EbenAET/Orciny-Device/circuit/kicad/orciny wiring RevB/orciny wiring RevB.kicad_pcb

## KiCad design electronic-exp-01-oscillator-integrator.kicad_sch

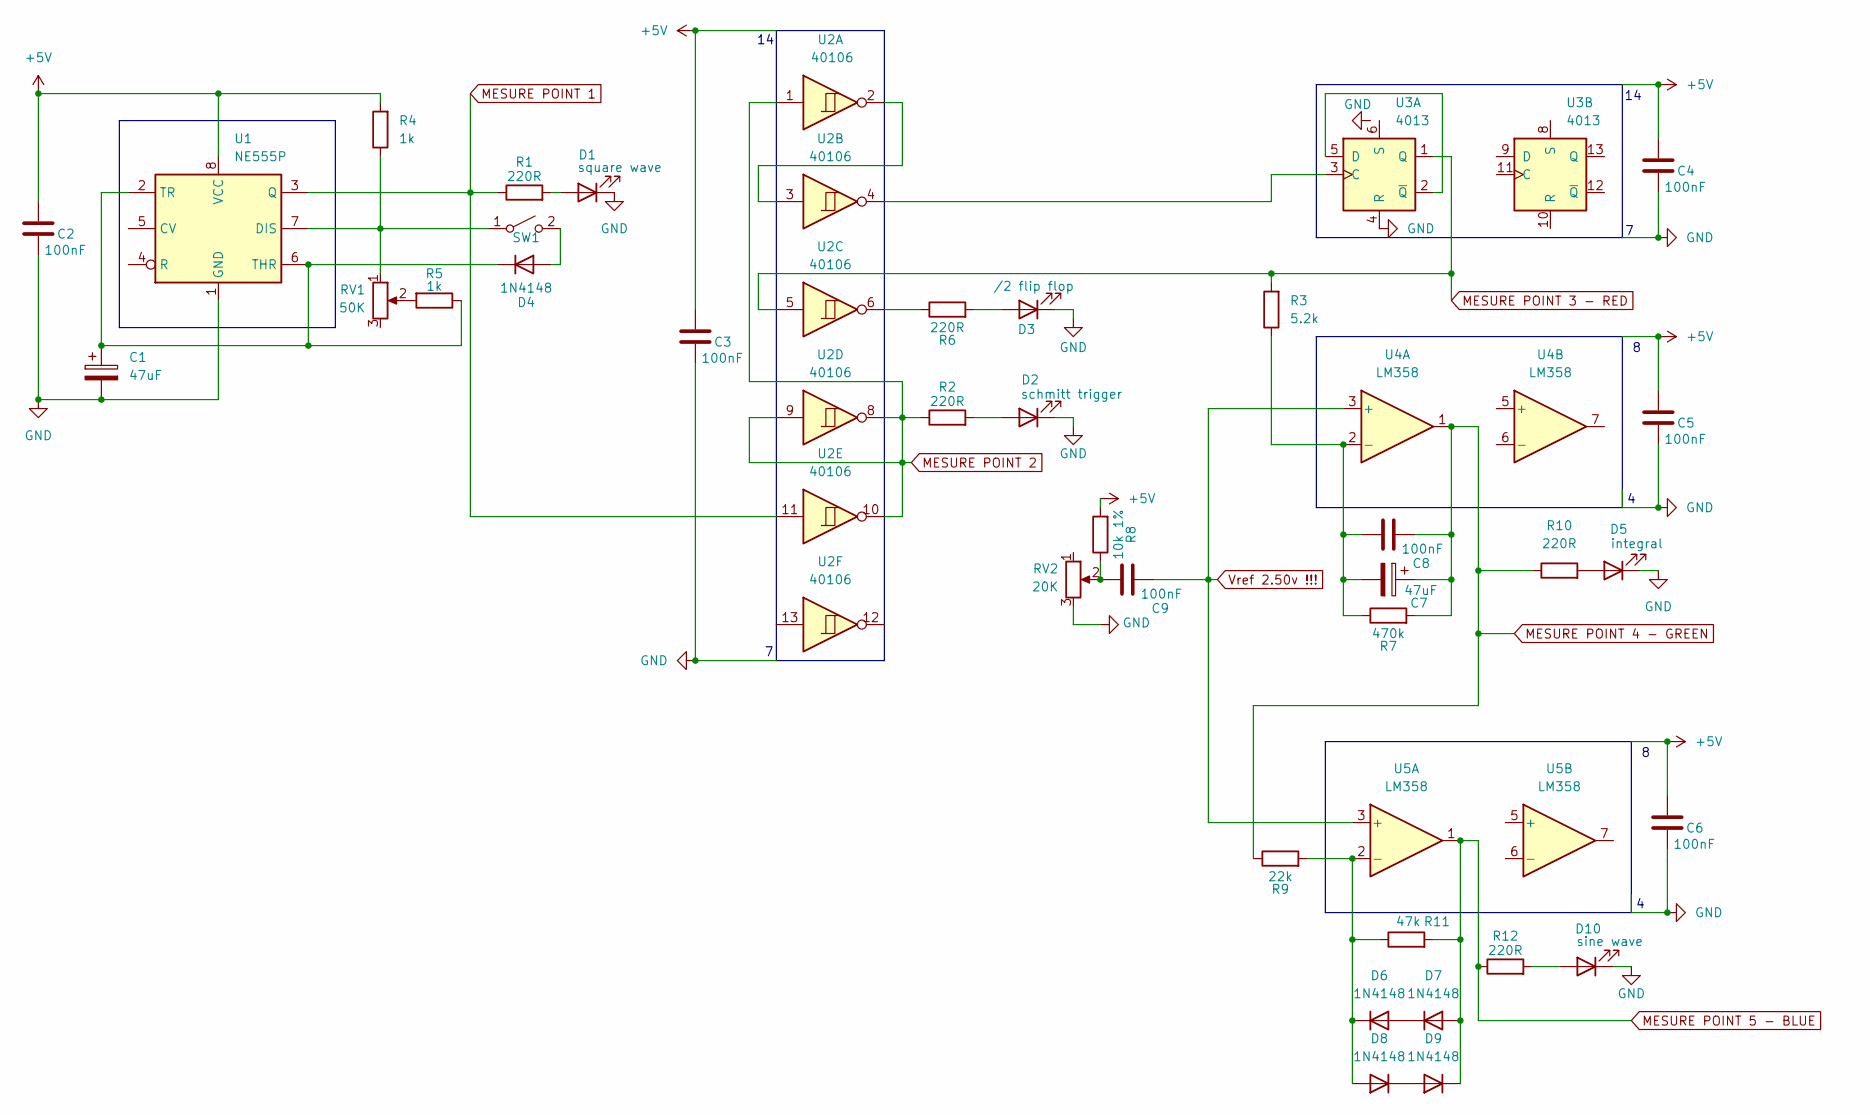
[picture p8: schematic electronic-exp-01-oscillator-integrator.kicad_sch]

Parts:
C1, C7: 47uF
C2, C3, C4, C5, C6, C8, C9: 100nF
D1: square wave
D2: schmitt trigger
D3: /2 flip flop
D4, D6, D7, D8, D9: 1N4148; D_DO-35_SOD27_P7.62mm_Horizontal
D5: integral
D10: sine wave
R1, R2, R6, R10, R12: 220R
R3: 5.2k
R4, R5: 1k
R7: 470k
R8: 10k 1%
R9: 22k
R11: 47k
RV1: 50K
RV2: 20K
SW1: (no value)
U1: NE555P; DIP-8_W7.62mm
U2: 40106
U3: 4013
U4, U5: LM358

Connections:
+5V: C2.1, C3.1, C4.1, C5.1, C6.1, R4.2, R8.2, U1.8 (VCC)
GND: C1.2, C2.2, C3.2, C4.2, C5.2, C6.2, D1.1 (K), D2.1 (K), D3.1 (K), D5.1 (K), D10.1 (K), RV2.3, U1.1 (GND), U3.4 (R)
MESURE POINT 1: R1.1, U1.3 (Q), U2.11
MESURE POINT 2: R2.1, U2.1, U2.8, U2.9, U2.10
MESURE POINT 3 - RED: R3.2, U2.5, U3.1 (Q)
MESURE POINT 4 - GREEN: C7.1, C8.1, R7.2, R9.1, R10.1, U4.1
MESURE POINT 5 - BLUE: D7.2 (A), D9.1 (K), R11.2, R12.1, U5.1
unnamed: C1.1, D4.1 (K), R5.1, U1.2 (TR), U1.6 (THR)
unnamed: C7.2, C8.2, R3.1, R7.1, U4.2 (-)
unnamed: C9.2, R8.1, RV2.2
unnamed: D1.2 (A), R1.2
unnamed: D2.2 (A), R2.2
unnamed: D3.2 (A), R6.2
unnamed: D4.2 (A), SW1.2 (B)
unnamed: D5.2 (A), R10.2
unnamed: D6.1 (K), D8.2 (A), R9.2, R11.1, U5.2 (-)
unnamed: D6.2 (A), D7.1 (K)
unnamed: D8.1 (K), D9.2 (A)
unnamed: D10.2 (A), R12.2
unnamed: R4.1, RV1.1, SW1.1 (A), U1.7 (DIS)
unnamed: R5.2, RV1.2
unnamed: R6.1, U2.6
unnamed: U2.2, U2.3
unnamed: U2.4, U3.3 (C)
unnamed: U3.2 (~Q), U3.5 (D)
Vref 2.50v !!!: C9.1, U4.3 (+), U5.3 (+)
