EbenAET/Orciny-Device/Arduino/rp2040_fx_controller_demo/rp2040_fx_controller_demo.ino

// =============================================================================
// rp2040_fx_controller_demo.ino
// Version : V 0.2.5
// Orciny Device — FX Controller  |  Demo / Testing Build
// Board : Adafruit Feather RP2040
// Wings : Prop-Maker FeatherWing + 8-Channel Servo FeatherWing (PCA9685)
// -----------------------------------------------------------------------------
// PURPOSE
//   This is the fully-commented demo version of the main FX controller sketch.
//   All logic is identical to the production sketch; comments have been added
//   throughout to explain every section for anyone reviewing or testing it.
//
// CONTROL PATH
//   Standalone mode only.
//   handleSwitches(), handleUsbCommands(), and buildActiveProfile() drive all
//   outputs directly from the physical buttons and USB serial commands.
//
// USB SERIAL COMMANDS (115200 baud, standalone mode)
//   help            — list all commands
//   status          — print power, sequence, and effect overrides
//   on / off        — enable or disable all outputs
//   toggle          — flip current output state
//   prev / next     — step through sequences
//   seq1 / seq2 / seq3 — jump directly to a numbered sequence
//   reset           — return to sequence 1, output off
//   sparks on|off|toggle|auto — per-effect override
//   spark1|spark2|spark3|spark4 on|off — force one spark channel for bench test
//   spark all on|off — force all spark channels on/off for bench test
//   spark status — print spark test mode and GPIO mapping
//   beam on|off|toggle|auto   — per-effect override
//   claw on|off|toggle|auto   — per-effect override
//   peltier on|off|auto|status — GP8 MOSFET gate override/test
//   red|green|blue on|off|toggle|auto — per-channel beam overrides
//   s|bm|c on|off|toggle|auto — short aliases for sparks|beam|claw
//   r|g|b on|off|toggle|auto  — short aliases for red|green|blue
//   beam palette cool|ember|cyan|violet|auto — beam colour palette
//   buttons         — print raw and debounced switch states
//   servoa/servob min|max|mid — direct PCA9685 channel test writes
//   neo on|off      — turn all pixels on (white) or off
//   neo color <R G B> [BRIGHT] — set all pixels to RGB color (0-255 each)
//   neo ember|pulse|beam|claw|show — test specific animation modes
//   neo auto        — follow scene default (stop testing)
//
// PHYSICAL CONTROLS
//   SW1 (A1 / GP27) — tap: toggle output on/off          (standalone only)
//   SW2 (A2 / GP28) — tap: step to previous sequence     (standalone only)
//   SW3 (A3 / GP29) — tap: step to next sequence         (standalone only)
//   SW1 + SW3 held 5 s — reset to sequence 1             (standalone only)
//
// DEMO SEQUENCES
//   1 — Ember  : sparks on, warm-orange NeoPixel ember glow    (beam: ember palette)
//   2 — Pulse  : beam pulsing, orange NeoPixel pulse           (beam: cool-white palette)
//   3 — Show   : sparks + beam + claw sweep, cyan NeoPixel     (beam: cyan palette)
// =============================================================================

#include <Adafruit_PWMServoDriver.h>  // PCA9685 servo wing driver
#include <Adafruit_NeoPixel.h>        // NeoPixel strip driver
#include <Wire.h>                     // I2C bus (required by servo driver)

#include <OrcinyCommon.h>              // Shared packet types: CoreFrame, EffectCommand, etc.
#include <ColorPalettes.h>             // Beam and NeoPixel color palettes
#include <AnimationPalettes.h>         // Animation preset definitions

#include "DeviceConfig.h"  // All pin assignments and tuning constants

// Pull frequently-used types into this file's scope so we don't have to
// prefix every usage with "orciny::".
using orciny::CoreFrame;
using orciny::EffectCommand;
using orciny::CoreMode;

// =============================================================================
// SEQUENCE IDs
// A SequenceId is just a named number.  It identifies which "scene" is active
// and drives the content of buildActiveProfile() below.
// =============================================================================
enum SequenceId : uint8_t {
  SEQUENCE_1 = 0,   // Ember scene
  SEQUENCE_2,       // Pulse scene
  SEQUENCE_3,       // Full show scene
  SEQUENCE_COUNT,   // Automatically equals the number of sequences (3)
};

// =============================================================================
// BEAM PALETTE IDs
// Named identifiers for the built-in beam colour palettes defined in
// DeviceConfig.h.  BEAM_PALETTE_AUTO means "use whatever the active scene
// requests"; the other values lock the palette regardless of scene.
// =============================================================================
enum BeamPaletteId : uint8_t {
  BEAM_PALETTE_AUTO = 0,   // follow the scene's palette selection
  BEAM_PALETTE_COOL,       // cool white (original swell colour)
  BEAM_PALETTE_EMBER,      // warm orange-red
  BEAM_PALETTE_CYAN,       // pure cyan
  BEAM_PALETTE_VIOLET,     // purple-violet
};

// Return the DeviceConfig palette for a given BeamPaletteId.
// BEAM_PALETTE_AUTO resolves to kPaletteCoolWhite (same as the original default).
const device_config::BeamPalette &getPaletteForId(BeamPaletteId id) {
  switch (id) {
    case BEAM_PALETTE_EMBER:  return device_config::kPaletteEmber;
    case BEAM_PALETTE_CYAN:   return device_config::kPaletteCyan;
    case BEAM_PALETTE_VIOLET: return device_config::kPaletteViolet;
    default:                  return device_config::kPaletteCoolWhite;
  }
}

// =============================================================================
// SceneProfile
// A flat data record that describes what every output subsystem should be doing
// for the currently active sequence.  buildActiveProfile() fills one of these;
// profileToEffectCommand() converts it into a wire-format EffectCommand.
// =============================================================================
struct SceneProfile {
  bool          sparksEnabled;
  uint8_t       sparksIntensity;   // 0–255 PWM brightness of random spark flashes
  bool          beamEnabled;       // Prop-Maker LED beam on/off
  bool          clawEnabled;       // Servo claw sweep on/off
  BeamPaletteId beamPaletteId;     // colour palette for the beam swell
  CoreFrame     coreFrame;         // NeoPixel core parameters (mode, color, speed…)
};

// =============================================================================
// MomentarySwitch
// Wraps a single digital input with software debouncing.
//
// Why debounce?  Mechanical switches bounce — the contacts open and close
// rapidly for ~5–20 ms after a press.  Without debouncing, one physical press
// can register as many events.  This class ignores transitions shorter than
// kSwitchDebounceMs before accepting them as stable.
//
// Usage:
//   switch.begin(PIN);         // call once in setup()
//   switch.update(millis());   // call every loop iteration
//   if (switch.wasPressed())   // true for exactly one loop after press
// =============================================================================
class MomentarySwitch {
 public:
  void begin(uint8_t pin) {
    pin_ = pin;
    pinMode(pin_, INPUT_PULLUP);  // Internal pull-up: floating = HIGH, pressed = LOW
    // Sample the physical state immediately so the first update() is accurate.
    const bool initialPressed = (digitalRead(pin_) == LOW);
    stablePressed_ = initialPressed;
    rawPressed_ = initialPressed;
    lastChangeMs_ = millis();
  }

  // Call once per loop iteration with the current millis() timestamp.
  void update(uint32_t now) {
    // Reset single-shot flags at the start of every update.
    pressedEvent_ = false;
    releasedEvent_ = false;

    const bool sampledPressed = (digitalRead(pin_) == LOW);

    // If the raw reading changed, restart the debounce timer.
    if (sampledPressed != rawPressed_) {
      rawPressed_ = sampledPressed;
      lastChangeMs_ = now;
    }

    // Wait for the signal to be stable for the full debounce window.
    if ((now - lastChangeMs_) < device_config::kSwitchDebounceMs) {
      return;  // Still within bouncing window — do nothing yet.
    }

    // If the stable state already matches the raw reading, nothing changed.
    if (stablePressed_ == rawPressed_) {
      return;
    }

    // The state changed and has been stable long enough — accept it.
    stablePressed_ = rawPressed_;
    if (stablePressed_) {
      pressedEvent_ = true;   // Fires on the loop after the press settles.
    } else {
      releasedEvent_ = true;  // Fires on the loop after the release settles.
    }
  }

  bool isPressed() const  { return stablePressed_; }  // Current stable state
  bool wasPressed() const { return pressedEvent_; }   // True for one loop on press
  bool wasReleased() const { return releasedEvent_; } // True for one loop on release

 private:
  uint8_t  pin_ = 0;
  bool     stablePressed_  = false;
  bool     rawPressed_     = false;
  bool     pressedEvent_   = false;
  bool     releasedEvent_  = false;
  uint32_t lastChangeMs_   = 0;
};

// =============================================================================
// SparkChannel
// Drives one GPIO pin with random PWM bursts to simulate a spark-gap element.
//
// Each channel independently decides when to fire and for how long using
// random timing windows.  The intensity parameter scales the peak brightness
// and also raises the floor so sparks never go completely dark during a flash.
// =============================================================================
class SparkChannel {
 public:
  void begin(uint8_t pin) {
    pin_ = pin;
    pinMode(pin_, OUTPUT);
    analogWrite(pin_, 0);  // Start off
    // Stagger the first event so all four channels don't fire simultaneously.
    nextEventMs_ = millis() + random(30, 180);
  }

  // enabled   : false forces pin low immediately and reschedules.
  // intensity : 0–255 PWM ceiling for peak brightness.
  void update(uint32_t now, bool enabled, uint8_t intensity) {
    if (!enabled) {
      analogWrite(pin_, 0);
      active_ = false;
      // Longer cool-down when disabled to prevent instant re-fire on enable.
      nextEventMs_ = now + random(80, 200);
      return;
    }

    if (active_) {
      // Currently in a flash burst — check whether the burst has expired.
      if (now >= flashUntilMs_) {
        active_ = false;
        analogWrite(pin_, 0);
        nextEventMs_ = now + random(25, 140);  // Random gap before next flash
      }
      return;  // Mid-burst: nothing to do until expiry.
    }

    // Waiting between flashes — check if it's time to fire.
    if (now < nextEventMs_) {
      return;
    }

    // Fire!  Choose a random PWM value between a floor and the intensity cap.
    const int minimum = max(32, intensity / 3);   // Minimum brightness floor
    const int peak    = max(minimum + 1, static_cast<int>(intensity) + 1);
    analogWrite(pin_, random(minimum, peak));
    // Hold the flash for a random short duration (20–70 ms).
    flashUntilMs_ = now + random(20, 71);
    active_ = true;
  }

  void setManualLevel(uint8_t level) {
    analogWrite(pin_, level);
    active_ = (level > 0);
  }

 private:
  uint8_t  pin_          = 0;
  bool     active_       = false;
  uint32_t nextEventMs_  = 0;
  uint32_t flashUntilMs_ = 0;
};

// =============================================================================
// BeamEffect
// Drives the three Prop-Maker MOSFET channels (Red/Green/Blue) with a slow
// sinusoidal swell whose colour is defined by a BeamPalette.
//
// The swell is computed from millis() so it runs continuously without a
// separate state machine.
//
// How the swell works:
//   • phase = (now % 2400) gives a 2.4-second repeating window (0–2399).
//   • First half (0–1199): linearly ramps from 100 → 255 (brightening).
//   • Second half (1200–2399): linearly ramps from 255 → 100 (dimming).
//   • Each RGB channel is scaled: output = (swell × palette.channel) / 255.
//   • Call setPalette() to change colour; defaults to kPaletteDefault.
// =============================================================================
class BeamEffect {
 public:
  void begin(uint8_t led1Pin, uint8_t led2Pin, uint8_t led3Pin) {
    redPin_   = led1Pin;
    greenPin_ = led2Pin;
    bluePin_  = led3Pin;
    pinMode(redPin_,   OUTPUT);
    pinMode(greenPin_, OUTPUT);
    pinMode(bluePin_,  OUTPUT);
    stop();
  }

  // Change the active colour palette.  Takes effect on the next update() call.
  void setPalette(const device_config::BeamPalette &palette) {
    currentPalette_ = palette;
  }

  void update(uint32_t now, bool enabled) {
    if (!enabled) {
      stop();
      return;
    }

    const uint16_t phase = now % 2400;  // 2.4-second cycle

    // Linear ramp up then down, staying in the 100–255 range.
    const uint8_t swell = phase < 1200
                          ? map(phase, 0,    1200, 100, 255)
                          : map(phase, 1200, 2400, 255, 100);

    // Scale each channel by (swell / 255) × palette peak value.
    const uint16_t s = swell;
    analogWrite(redPin_,   static_cast<uint8_t>((s * currentPalette_.red)   / 255));
    analogWrite(greenPin_, static_cast<uint8_t>((s * currentPalette_.green) / 255));
    analogWrite(bluePin_,  static_cast<uint8_t>((s * currentPalette_.blue)  / 255));
    active_ = true;
  }

  void stop() {
    analogWrite(redPin_,   0);
    analogWrite(greenPin_, 0);
    analogWrite(bluePin_,  0);
    active_ = false;
  }

 private:
  uint8_t redPin_   = 0;
  uint8_t greenPin_ = 0;
  uint8_t bluePin_  = 0;
  bool    active_   = false;
  device_config::BeamPalette currentPalette_ = device_config::kPaletteDefault;
};

// =============================================================================
// ClawEffect
// Drives two servo channels on the PCA9685 in a continuous back-and-forth sweep.
//
// Servo A sweeps from minAngleA to maxAngleA and back.
// Servo B mirrors Servo A using a cross-mapped angle so both claw halves open
// and close together (one going up while the other goes down).
//
// The step interval (kClawStepIntervalMs) controls how fast the claw sweeps.
// Each update() call advances the angle by exactly one degree if the interval
// has elapsed — no delays or blocking waits.
// =============================================================================
class ClawEffect {
 public:
  void begin(Adafruit_PWMServoDriver &driver,
             uint8_t servoChannelA, uint8_t servoChannelB,
             uint8_t minAngleA,    uint8_t maxAngleA,
             uint8_t minAngleB,    uint8_t maxAngleB) {
    driver_        = &driver;
    servoChannelA_ = servoChannelA;
    servoChannelB_ = servoChannelB;
    // Ensure min < max regardless of which way the caller passed them.
    minAngleA_ = min(minAngleA, maxAngleA);
    maxAngleA_ = max(minAngleA, maxAngleA);
    minAngleB_ = min(minAngleB, maxAngleB);
    maxAngleB_ = max(minAngleB, maxAngleB);
    angle_     = minAngleA_;
    direction_ = 1;             // Start sweeping toward maxAngleA_
    active_    = false;
    wasEnabled_ = false;
    if (device_config::kServoIdleWhenInactive) {
      idleServos();
    } else {
      writeServos(static_cast<uint8_t>(angle_));
      active_ = true;
    }
  }

  void update(uint32_t now, bool enabled) {
    if (!enabled) {
      if (wasEnabled_) {
        stop();
      }
      wasEnabled_ = false;
      return;
    }

    if (!wasEnabled_) {
      writeServos(static_cast<uint8_t>(angle_));
      nextStepMs_  = now + device_config::kClawStepIntervalMs;
      active_      = true;
      wasEnabled_  = true;
      return;
    }

    // Non-blocking timer: only advance one step after the interval elapses.
    if (now < nextStepMs_) {
      return;
    }

    angle_ += direction_;

    // Reverse direction at each travel limit.
    if (angle_ >= maxAngleA_) {
      angle_     = maxAngleA_;
      direction_ = -1;
    } else if (angle_ <= minAngleA_) {
      angle_     = minAngleA_;
      direction_ = 1;
    }

    writeServos(static_cast<uint8_t>(angle_));
    nextStepMs_ = now + device_config::kClawStepIntervalMs;
    active_ = true;
  }

  // Disable or park claw servos when motion is inactive.
  void stop() {
    if (!active_) {
      return;  // Already stopped — avoid redundant I2C writes.
    }

    if (device_config::kServoIdleWhenInactive) {
      idleServos();
    } else {
      writeServos(minAngleA_);
    }

    active_ = false;
  }

 private:
  // Convert a 0–180° angle to the PCA9685 pulse-count range.
  uint16_t angleToPulse(uint8_t angle) const {
    return map(angle, 0, 180,
               device_config::kServoMinPulse,
               device_config::kServoMaxPulse);
  }

  // Mirror Servo A's angle onto Servo B's range so they move in opposition.
  uint8_t mapAngleForB(uint8_t angleA) const {
    return map(angleA, minAngleA_, maxAngleA_, maxAngleB_, minAngleB_);
  }

  // Push both servo positions to the PCA9685 over I2C.
  void writeServos(uint8_t angleA) {
    if (driver_ == nullptr) {
      return;
    }
    const uint8_t clampedA = constrain(angleA, minAngleA_, maxAngleA_);
    const uint8_t angleB   = constrain(mapAngleForB(clampedA), minAngleB_, maxAngleB_);
    driver_->setPWM(servoChannelA_, 0, angleToPulse(clampedA));
    driver_->setPWM(servoChannelB_, 0, angleToPulse(angleB));
  }

  // PCA9685 off command for a channel: ON=0/OFF=0 disables pulses.
  void idleServos() {
    if (driver_ == nullptr) {
      return;
    }
    driver_->setPWM(servoChannelA_, 0, 0);
    driver_->setPWM(servoChannelB_, 0, 0);
  }

  Adafruit_PWMServoDriver *driver_ = nullptr;
  uint8_t  servoChannelA_ = 0;
  uint8_t  servoChannelB_ = 1;
  int16_t  angle_         = 0;
  uint8_t  minAngleA_     = 0;
  uint8_t  maxAngleA_     = 180;
  uint8_t  minAngleB_     = 0;
  uint8_t  maxAngleB_     = 180;
  int8_t   direction_     = 1;
  bool     active_        = false;
  bool     wasEnabled_    = false;
  uint32_t nextStepMs_    = 0;
};

// =============================================================================
// GLOBAL INSTANCES
// One object per physical subsystem.  All are initialized in setup().
// =============================================================================

SparkChannel sparks[device_config::kSparkCount];  // Four independent spark channels
BeamEffect   beamEffect;                           // Prop-Maker RGB beam
ClawEffect   clawEffect;                           // Dual-servo claw
Adafruit_PWMServoDriver servoDriver(device_config::kServoDriverI2cAddress);
Adafruit_NeoPixel neoPixelStrip(device_config::kNeoPixelCount,
                                device_config::kNeoPixelPin,
                                device_config::kNeoPixelType);

MomentarySwitch powerSwitch;    // SW1 — on/off toggle
MomentarySwitch previousSwitch; // SW2 — previous sequence
MomentarySwitch nextSwitch;     // SW3 — next sequence

// =============================================================================
// GLOBAL STATE VARIABLES
// These track the runtime state; they are manipulated by the standalone-mode
// control functions (handleSwitches, handleUsbCommands).
// =============================================================================

SequenceId currentSequence      = SEQUENCE_1;  // Which scene is active
bool       outputEnabled        = false;         // Master on/off flag

enum EffectOverride : uint8_t {
  OVERRIDE_AUTO = 0,
  OVERRIDE_FORCE_OFF,
  OVERRIDE_FORCE_ON,
};

EffectOverride sparksOverride = OVERRIDE_AUTO;
EffectOverride beamOverride   = OVERRIDE_AUTO;
EffectOverride clawOverride   = OVERRIDE_AUTO;
EffectOverride peltierOverride = OVERRIDE_AUTO;
EffectOverride beamRedOverride   = OVERRIDE_AUTO;
EffectOverride beamGreenOverride = OVERRIDE_AUTO;
EffectOverride beamBlueOverride  = OVERRIDE_AUTO;
int8_t sparkTestSelection = -1;  // -1=auto, 0..3=single channel, 4=all channels

// Active beam palette override.  BEAM_PALETTE_AUTO uses the active scene's default.
BeamPaletteId beamPaletteOverride = BEAM_PALETTE_AUTO;

// Active NeoPixel frame override. Mode OFF means "use scene default".
CoreFrame neoPixelOverride = orciny::defaultFrame();

// USB receive buffer — characters accumulate here until a newline is received.
String usbCommandBuffer;

uint32_t peltierHoldUntilMs  = 0;  // Keep cooling active briefly after beam-off

// Standalone-only build always reports standalone mode.
bool standaloneMode = true;

bool     suppressPreviousRelease = false;

// State for the SW1+SW3 reset chord (standalone mode only).
uint32_t resetChordStartMs    = 0;
bool     resetChordTriggered  = false;
bool     suppressPowerRelease = false;  // Prevent toggle fire after chord hold
bool     suppressNextRelease  = false;  // Prevent seq advance after chord hold

// =============================================================================
// UTILITY — status printing
// =============================================================================

// Print a list of available USB serial commands.
void printHelp() {
  Serial.println(F("Commands: help, status, on, off, toggle, prev, next, seq1, seq2, seq3, reset"));
  Serial.println(F("         sparks on|off|toggle|auto"));
  Serial.println(F("         spark1|spark2|spark3|spark4 on|off"));
  Serial.println(F("         spark all on|off"));
  Serial.println(F("         spark status"));
  Serial.println(F("         beam   on|off|toggle|auto"));
  Serial.println(F("         claw   on|off|toggle|auto"));
  Serial.println(F("         peltier on|off|auto|status"));
  Serial.println(F("         red|green|blue on|off|toggle|auto"));
  Serial.println(F("         s|bm|c and r|g|b on|off|toggle|auto"));
  Serial.println(F("         beam palette cool|ember|cyan|violet|auto"));
  Serial.println(F("         buttons"));
  Serial.println(F("         servoa min|max|mid"));
  Serial.println(F("         servob min|max|mid"));
  Serial.println(F("         neo on|off|color <R G B> [BRIGHT]"));
  Serial.println(F("         neo ember|pulse|beam|claw|show|auto"));
}

uint16_t servoAngleToPulse(uint8_t angle) {
  return map(angle, 0, 180, device_config::kServoMinPulse, device_config::kServoMaxPulse);
}

void writeServoTest(uint8_t channel, uint8_t angle) {
  servoDriver.setPWM(channel, 0, servoAngleToPulse(angle));
  Serial.print(F("Servo CH"));
  Serial.print(channel);
  Serial.print(F(" -> angle "));
  Serial.println(angle);
}

void printButtonSnapshot() {
  const bool rawSw1Pressed = digitalRead(device_config::kPowerSwitchPin) == LOW;
  const bool rawSw2Pressed = digitalRead(device_config::kPreviousSwitchPin) == LOW;
  const bool rawSw3Pressed = digitalRead(device_config::kNextSwitchPin) == LOW;

  Serial.print(F("Buttons raw      -> SW1:"));
  Serial.print(rawSw1Pressed ? F("P") : F("R"));
  Serial.print(F(" SW2:"));
  Serial.print(rawSw2Pressed ? F("P") : F("R"));
  Serial.print(F(" SW3:"));
  Serial.println(rawSw3Pressed ? F("P") : F("R"));

  Serial.print(F("Buttons debounced-> SW1:"));
  Serial.print(powerSwitch.isPressed() ? F("P") : F("R"));
  Serial.print(F(" SW2:"));
  Serial.print(previousSwitch.isPressed() ? F("P") : F("R"));
  Serial.print(F(" SW3:"));
  Serial.println(nextSwitch.isPressed() ? F("P") : F("R"));
}

const __FlashStringHelper *overrideLabel(EffectOverride value) {
  switch (value) {
    case OVERRIDE_FORCE_OFF: return F("FORCE_OFF");
    case OVERRIDE_FORCE_ON:  return F("FORCE_ON");
    default:                 return F("AUTO");
  }
}

bool applyOverride(bool baseState, EffectOverride value) {
  if (value == OVERRIDE_FORCE_ON) {
    return true;
  }
  if (value == OVERRIDE_FORCE_OFF) {
    return false;
  }
  return baseState;
}

bool isSparkTestActive() {
  return sparkTestSelection >= 0;
}

bool isSparkTestChannelEnabled(uint8_t index) {
  return sparkTestSelection == device_config::kSparkCount ||
         sparkTestSelection == static_cast<int8_t>(index);
}

void printSparkTestStatus() {
  if (!isSparkTestActive()) {
    Serial.println(F("Spark test -> AUTO"));
    return;
  }

  if (sparkTestSelection == device_config::kSparkCount) {
    Serial.println(F("Spark test -> ALL ON"));
    return;
  }

  Serial.print(F("Spark test -> CH"));
  Serial.print(sparkTestSelection + 1);
  Serial.println(F(" ON"));
}

void printSparkPinMap() {
  Serial.print(F("Spark pins -> CH1:GP"));
  Serial.print(device_config::kSparkPins[0]);
  Serial.print(F(" CH2:GP"));
  Serial.print(device_config::kSparkPins[1]);
  Serial.print(F(" CH3:GP"));
  Serial.print(device_config::kSparkPins[2]);
  Serial.print(F(" CH4:GP"));
  Serial.println(device_config::kSparkPins[3]);
}

void printSparkStatus() {
  printSparkTestStatus();
  printSparkPinMap();
}

void printPeltierStatus() {
  Serial.print(F("Peltier -> "));
  Serial.print(overrideLabel(peltierOverride));
  Serial.print(F(", GP"));
  Serial.print(device_config::kPeltierControlPin);
  Serial.print(F(" pin is "));
  Serial.println(digitalRead(device_config::kPeltierControlPin) == HIGH ? F("HIGH") : F("LOW"));
}

void printModeStatus() {
  Serial.println(F("Mode -> STANDALONE"));
}

void printOverrideStatus() {
  Serial.print(F("Overrides -> sparks: "));
  Serial.print(overrideLabel(sparksOverride));
  Serial.print(F(", beam: "));
  Serial.print(overrideLabel(beamOverride));
  Serial.print(F(", claw: "));
  Serial.print(overrideLabel(clawOverride));
  Serial.print(F(", peltier: "));
  Serial.println(overrideLabel(peltierOverride));

  Serial.print(F("Beam RGB -> R: "));
  Serial.print(overrideLabel(beamRedOverride));
  Serial.print(F(", G: "));
  Serial.print(overrideLabel(beamGreenOverride));
  Serial.print(F(", B: "));
  Serial.println(overrideLabel(beamBlueOverride));

  const __FlashStringHelper *palLabel;
  switch (beamPaletteOverride) {
    case BEAM_PALETTE_COOL:   palLabel = F("cool");   break;
    case BEAM_PALETTE_EMBER:  palLabel = F("ember");  break;
    case BEAM_PALETTE_CYAN:   palLabel = F("cyan");   break;
    case BEAM_PALETTE_VIOLET: palLabel = F("violet"); break;
    default:                  palLabel = F("auto");   break;
  }
  Serial.print(F("Beam palette -> "));
  Serial.println(palLabel);
  printSparkTestStatus();
}

// Print the current power state and sequence number to USB serial.
void printSequenceStatus() {
  printModeStatus();
  Serial.print(F("Power -> "));
  Serial.print(outputEnabled ? F("ON") : F("OFF"));
  Serial.print(F(", Sequence -> "));
  Serial.println(static_cast<uint8_t>(currentSequence) + 1);
  printOverrideStatus();
  printButtonSnapshot();
}

// =============================================================================
// SCENE PROFILES
// buildActiveProfile() is the heart of standalone mode.  It maps the current
// (outputEnabled, currentSequence) state to a full SceneProfile that describes
// what every subsystem should do.
//
// Add or modify cases here to change what each button-selectable scene does.
// This function is the active profile source for this standalone-only build.
// =============================================================================
SceneProfile buildActiveProfile() {
  SceneProfile profile = {};
  profile.coreFrame = orciny::defaultFrame();

  // Output off — zero everything and return early.
  if (!outputEnabled) {
    profile.coreFrame.mode       = orciny::CORE_MODE_OFF;
    profile.coreFrame.brightness = 0;
    return profile;
  }

  switch (currentSequence) {

    // --- SEQUENCE 1: Ember ---------------------------------------------------
    // Sparks flash at high intensity.  NeoPixel glows a warm orange ember.
    case SEQUENCE_1:
      profile.sparksEnabled    = true;
      profile.sparksIntensity  = 220;
      profile.beamPaletteId        = BEAM_PALETTE_EMBER;
      profile.coreFrame.mode       = orciny::CORE_MODE_EMBER;
      profile.coreFrame.brightness = 56;
      profile.coreFrame.speed      = 90;
      profile.coreFrame.red        = 255;
      profile.coreFrame.green      = 110;
      profile.coreFrame.blue       = 24;
      return profile;

    // --- SEQUENCE 2: Pulse ---------------------------------------------------
    // Beam lamp cycles on/off.  NeoPixel pulses in a cooler orange.
    case SEQUENCE_2:
      profile.beamEnabled          = true;
      profile.beamPaletteId        = BEAM_PALETTE_COOL;
      profile.coreFrame.mode       = orciny::CORE_MODE_PULSE;
      profile.coreFrame.brightness = 96;
      profile.coreFrame.speed      = 110;
      profile.coreFrame.red        = 255;
      profile.coreFrame.green      = 48;
      profile.coreFrame.blue       = 0;
      return profile;

    // --- SEQUENCE 3: Full Show -----------------------------------------------
    // Everything on: sparks at max, beam running, claw sweeping, NeoPixel show.
    case SEQUENCE_3:
      profile.sparksEnabled    = true;
      profile.sparksIntensity  = 255;
      profile.beamEnabled      = true;
      profile.beamPaletteId    = BEAM_PALETTE_CYAN;
      profile.clawEnabled      = true;
      profile.coreFrame.mode       = orciny::CORE_MODE_SHOW;
      profile.coreFrame.brightness = 180;
      profile.coreFrame.speed      = 140;
      profile.coreFrame.red        = 60;
      profile.coreFrame.green      = 220;
      profile.coreFrame.blue       = 255;
      return profile;

    default:
      profile.coreFrame.mode       = orciny::CORE_MODE_OFF;
      profile.coreFrame.brightness = 0;
      return profile;
  }
}

// Convert a SceneProfile into an EffectCommand so updateEffects() can consume
// a single, consistent command structure.
EffectCommand profileToEffectCommand(const SceneProfile &profile) {
  EffectCommand command = orciny::defaultEffectCommand();
  command.outputEnabled   = outputEnabled;
  command.sparksEnabled   = applyOverride(profile.sparksEnabled, sparksOverride);
  command.sparksIntensity = command.sparksEnabled
                            ? (profile.sparksIntensity > 0 ? profile.sparksIntensity : 220)
                            : 0;
  command.pulseEnabled    = false;  // Not used in current hardware
  command.beamEnabled     = applyOverride(profile.beamEnabled, beamOverride);
  command.clawEnabled     = applyOverride(profile.clawEnabled, clawOverride);
  return command;
}

// =============================================================================
// SEQUENCE NAVIGATION HELPERS
// =============================================================================

SequenceId previousSequenceValue(SequenceId sequence) {
  // Wrap around: sequence 1 → wraps back to sequence 3.
  return sequence == SEQUENCE_1 ? SEQUENCE_3
                                : static_cast<SequenceId>(sequence - 1);
}

SequenceId nextSequenceValue(SequenceId sequence) {
  // Wrap around: sequence 3 → wraps back to sequence 1.
  return sequence == SEQUENCE_3 ? SEQUENCE_1
                                : static_cast<SequenceId>(sequence + 1);
}

void setSequence(SequenceId sequence) {
  currentSequence = sequence;
  printSequenceStatus();  // Echo new state to USB serial
}

void resetToBeginning() {
  currentSequence = SEQUENCE_1;
  outputEnabled = false;
  sparksOverride = OVERRIDE_AUTO;
  beamOverride = OVERRIDE_AUTO;
  clawOverride = OVERRIDE_AUTO;
  peltierOverride = OVERRIDE_AUTO;
  beamRedOverride = OVERRIDE_AUTO;
  beamGreenOverride = OVERRIDE_AUTO;
  beamBlueOverride = OVERRIDE_AUTO;
  beamPaletteOverride = BEAM_PALETTE_AUTO;
  Serial.println(F("Reset -> sequence 1"));
  printSequenceStatus();
}

// =============================================================================
// STANDALONE MODE — USB SERIAL COMMAND HANDLER
// Reads characters from USB Serial one at a time and processes complete lines.
// Call this from loop() to enable USB debug control (standalone mode only).
// =============================================================================
void handleUsbCommands() {
  while (Serial.available() > 0) {
    const char incoming = static_cast<char>(Serial.read());
    if (incoming == '\r') {
      continue;  // Skip Windows carriage-return characters
    }
    if (incoming != '\n') {
      usbCommandBuffer += incoming;  // Accumulate until newline
      continue;
    }

    // Newline received — process the buffered line.
    String command = usbCommandBuffer;
    usbCommandBuffer = "";
    command.trim();
    command.toLowerCase();

    if (command.length() == 0) {
      continue;  // Ignore blank lines
    }

    if      (command == F("help"))   { printHelp(); }
    else if (command == F("status")) { printSequenceStatus(); }
    else if (command == F("on"))     { outputEnabled = true;              printSequenceStatus(); }
    else if (command == F("off"))    { outputEnabled = false;             printSequenceStatus(); }
    else if (command == F("toggle")) { outputEnabled = !outputEnabled;    printSequenceStatus(); }
    else if (command == F("prev"))   { setSequence(previousSequenceValue(currentSequence)); }
    else if (command == F("next"))   { setSequence(nextSequenceValue(currentSequence)); }
    else if (command == F("seq1"))   { setSequence(SEQUENCE_1); }
    else if (command == F("seq2"))   { setSequence(SEQUENCE_2); }
    else if (command == F("seq3"))   { setSequence(SEQUENCE_3); }
    else if (command == F("reset"))  { resetToBeginning(); }
    else if (command == F("buttons")) { printButtonSnapshot(); }
    else if (command == F("sparks on") || command == F("s on"))     { sparksOverride = OVERRIDE_FORCE_ON;  printOverrideStatus(); }
    else if (command == F("sparks off") || command == F("s off"))    { sparksOverride = OVERRIDE_FORCE_OFF; printOverrideStatus(); }
    else if (command == F("sparks auto") || command == F("s auto"))   { sparksOverride = OVERRIDE_AUTO;      printOverrideStatus(); }
    else if (command == F("sparks toggle") || command == F("s toggle")) {
      sparksOverride = (sparksOverride == OVERRIDE_FORCE_ON) ? OVERRIDE_FORCE_OFF : OVERRIDE_FORCE_ON;
      printOverrideStatus();
    }
    else if (command == F("spark1 on")) { sparkTestSelection = 0; printSparkStatus(); }
    else if (command == F("spark2 on")) { sparkTestSelection = 1; printSparkStatus(); }
    else if (command == F("spark3 on")) { sparkTestSelection = 2; printSparkStatus(); }
    else if (command == F("spark4 on")) { sparkTestSelection = 3; printSparkStatus(); }
    else if (command == F("spark1 off") || command == F("spark2 off") ||
             command == F("spark3 off") || command == F("spark4 off") ||
             command == F("spark all off") || command == F("spark off")) {
      sparkTestSelection = -1;
      printSparkStatus();
    }
    else if (command == F("spark all on")) {
      sparkTestSelection = device_config::kSparkCount;
      printSparkStatus();
    }
    else if (command == F("spark status")) { printSparkStatus(); }
    else if (command == F("beam on") || command == F("bm on"))       { beamOverride = OVERRIDE_FORCE_ON;    printOverrideStatus(); }
    else if (command == F("beam off") || command == F("bm off"))      { beamOverride = OVERRIDE_FORCE_OFF;   printOverrideStatus(); }
    else if (command == F("beam auto") || command == F("bm auto"))     { beamOverride = OVERRIDE_AUTO;        printOverrideStatus(); }
    else if (command == F("beam toggle") || command == F("bm toggle")) {
      beamOverride = (beamOverride == OVERRIDE_FORCE_ON) ? OVERRIDE_FORCE_OFF : OVERRIDE_FORCE_ON;
      printOverrideStatus();
    }
    else if (command == F("claw on") || command == F("c on"))       { clawOverride = OVERRIDE_FORCE_ON;    printOverrideStatus(); }
    else if (command == F("claw off") || command == F("c off"))      { clawOverride = OVERRIDE_FORCE_OFF;   printOverrideStatus(); }
    else if (command == F("claw auto") || command == F("c auto"))     { clawOverride = OVERRIDE_AUTO;        printOverrideStatus(); }
    else if (command == F("claw toggle") || command == F("c toggle")) {
      clawOverride = (clawOverride == OVERRIDE_FORCE_ON) ? OVERRIDE_FORCE_OFF : OVERRIDE_FORCE_ON;
      printOverrideStatus();
    }
    else if (command == F("peltier on") || command == F("pel on")) {
      peltierOverride = OVERRIDE_FORCE_ON;
      peltierHoldUntilMs = millis() + device_config::kPeltierPostBeamHoldMs;
      printPeltierStatus();
    }
    else if (command == F("peltier off") || command == F("pel off")) {
      peltierOverride = OVERRIDE_FORCE_OFF;
      peltierHoldUntilMs = 0;
      printPeltierStatus();
    }
    else if (command == F("peltier auto") || command == F("pel auto")) {
      peltierOverride = OVERRIDE_AUTO;
      printPeltierStatus();
    }
    else if (command == F("peltier status") || command == F("pel status")) {
      printPeltierStatus();
    }
    else if (command == F("servoa min")) { writeServoTest(device_config::kServoChannelA, device_config::kServoAMinAngle); }
    else if (command == F("servoa max")) { writeServoTest(device_config::kServoChannelA, device_config::kServoAMaxAngle); }
    else if (command == F("servoa mid")) { writeServoTest(device_config::kServoChannelA, (device_config::kServoAMinAngle + device_config::kServoAMaxAngle) / 2); }
    else if (command == F("servob min")) { writeServoTest(device_config::kServoChannelB, device_config::kServoBMinAngle); }
    else if (command == F("servob max")) { writeServoTest(device_config::kServoChannelB, device_config::kServoBMaxAngle); }
    else if (command == F("servob mid")) { writeServoTest(device_config::kServoChannelB, (device_config::kServoBMinAngle + device_config::kServoBMaxAngle) / 2); }
    else if (command == F("red on") || command == F("r on"))         { beamRedOverride = OVERRIDE_FORCE_ON;   printOverrideStatus(); }
    else if (command == F("red off") || command == F("r off"))        { beamRedOverride = OVERRIDE_FORCE_OFF;  printOverrideStatus(); }
    else if (command == F("red auto") || command == F("r auto"))      { beamRedOverride = OVERRIDE_AUTO;       printOverrideStatus(); }
    else if (command == F("red toggle") || command == F("r toggle")) {
      beamRedOverride = (beamRedOverride == OVERRIDE_FORCE_ON) ? OVERRIDE_FORCE_OFF : OVERRIDE_FORCE_ON;
      printOverrideStatus();
    }
    else if (command == F("green on") || command == F("g on"))         { beamGreenOverride = OVERRIDE_FORCE_ON;   printOverrideStatus(); }
    else if (command == F("green off") || command == F("g off"))        { beamGreenOverride = OVERRIDE_FORCE_OFF;  printOverrideStatus(); }
    else if (command == F("green auto") || command == F("g auto"))      { beamGreenOverride = OVERRIDE_AUTO;       printOverrideStatus(); }
    else if (command == F("green toggle") || command == F("g toggle")) {
      beamGreenOverride = (beamGreenOverride == OVERRIDE_FORCE_ON) ? OVERRIDE_FORCE_OFF : OVERRIDE_FORCE_ON;
      printOverrideStatus();
    }
    else if (command == F("blue on") || command == F("b on"))         { beamBlueOverride = OVERRIDE_FORCE_ON;   printOverrideStatus(); }
    else if (command == F("blue off") || command == F("b off"))        { beamBlueOverride = OVERRIDE_FORCE_OFF;  printOverrideStatus(); }
    else if (command == F("blue auto") || command == F("b auto"))      { beamBlueOverride = OVERRIDE_AUTO;       printOverrideStatus(); }
    else if (command == F("blue toggle") || command == F("b toggle")) {
      beamBlueOverride = (beamBlueOverride == OVERRIDE_FORCE_ON) ? OVERRIDE_FORCE_OFF : OVERRIDE_FORCE_ON;
      printOverrideStatus();
    }
    else if (command == F("beam palette cool")   || command == F("bm pal cool"))   { beamPaletteOverride = BEAM_PALETTE_COOL;   printOverrideStatus(); }
    else if (command == F("beam palette ember")  || command == F("bm pal ember"))  { beamPaletteOverride = BEAM_PALETTE_EMBER;  printOverrideStatus(); }
    else if (command == F("beam palette cyan")   || command == F("bm pal cyan"))   { beamPaletteOverride = BEAM_PALETTE_CYAN;   printOverrideStatus(); }
    else if (command == F("beam palette violet") || command == F("bm pal violet")) { beamPaletteOverride = BEAM_PALETTE_VIOLET; printOverrideStatus(); }
    else if (command == F("beam palette auto")   || command == F("bm pal auto"))   { beamPaletteOverride = BEAM_PALETTE_AUTO;   printOverrideStatus(); }

    // --- NeoPixel test commands ------------------------------------------------
    else if (command == F("neo off")) {
      neoPixelStrip.clear();
      neoPixelStrip.show();
      Serial.println(F("Neo: OFF"));
    }
    else if (command == F("neo on")) {
      for (uint16_t i = 0; i < neoPixelStrip.numPixels(); ++i) {
        neoPixelStrip.setPixelColor(i, neoPixelStrip.Color(64, 64, 64));
      }
      neoPixelStrip.show();
      Serial.println(F("Neo: all white"));
    }
    else if (command.startsWith(F("neo color "))) {
      // Parse "neo color R G B" or "neo color R G B BRIGHTNESS"
      String args = command.substring(10);
      int r = 0, g = 0, b = 0, bright = 255;
      int parsed = sscanf(args.c_str(), "%d %d %d %d", &r, &g, &b, &bright);
      if (parsed >= 3) {
        r = constrain(r, 0, 255);
        g = constrain(g, 0, 255);
        b = constrain(b, 0, 255);
        bright = constrain(bright, 0, 255);
        for (uint16_t i = 0; i < neoPixelStrip.numPixels(); ++i) {
          neoPixelStrip.setPixelColor(i, neoPixelStrip.Color(
              (r * bright) / 255, (g * bright) / 255, (b * bright) / 255));
        }
        neoPixelStrip.show();
        Serial.print(F("Neo: RGB "));
        Serial.print(r); Serial.print(F(" "));
        Serial.print(g); Serial.print(F(" "));
        Serial.print(b); Serial.print(F(" @ "));
        Serial.println(bright);
      } else {
        Serial.println(F("Usage: neo color <R 0-255> <G 0-255> <B 0-255> [BRIGHT 0-255]"));
      }
    }
    else if (command == F("neo ember") || command == F("neo pulse") || 
             command == F("neo beam") || command == F("neo claw") ||
             command == F("neo show")) {
      // Test specific modes
      CoreFrame testFrame = orciny::defaultFrame();
      if (command == F("neo ember")) { testFrame.mode = orciny::CORE_MODE_EMBER; testFrame.brightness = 120; }
      else if (command == F("neo pulse")) { testFrame.mode = orciny::CORE_MODE_PULSE; testFrame.brightness = 200; }
      else if (command == F("neo beam")) { testFrame.mode = orciny::CORE_MODE_BEAM; testFrame.brightness = 150; }
      else if (command == F("neo claw")) { testFrame.mode = orciny::CORE_MODE_CLAW; testFrame.brightness = 100; }
      else if (command == F("neo show")) { testFrame.mode = orciny::CORE_MODE_SHOW; testFrame.brightness = 100; }
      neoPixelOverride = testFrame;
      Serial.print(F("Neo: testing mode "));
      Serial.println(static_cast<uint8_t>(testFrame.mode));
    }
    else if (command == F("neo auto")) {
      neoPixelOverride.mode = orciny::CORE_MODE_OFF;  // Signal to use scene default
      Serial.println(F("Neo: auto (follow scene)"));
    }

    else {
      Serial.print(F("Unknown command: "));
      Serial.println(command);
      printHelp();
    }
  }
}

// =============================================================================
// PHYSICAL SWITCH HANDLER
// Updates all three switch debouncers and processes chord / button events.
// Called every loop iteration.
// =============================================================================
void handleSwitches(uint32_t now) {
  // Update all three switch debounce state machines.
  powerSwitch.update(now);
  previousSwitch.update(now);
  nextSwitch.update(now);

  if (powerSwitch.wasPressed() || powerSwitch.wasReleased() ||
      previousSwitch.wasPressed() || previousSwitch.wasReleased() ||
      nextSwitch.wasPressed() || nextSwitch.wasReleased()) {
    printButtonSnapshot();
  }

  // --- Reset chord: SW1 + SW3 held for kResetHoldMs (standalone only) ------
  const bool resetChordDown = powerSwitch.isPressed() && nextSwitch.isPressed();

  if (resetChordDown) {
    if (resetChordStartMs == 0) {
      resetChordStartMs    = now;
      suppressPowerRelease = true;  // Don't fire toggle on chord release
      suppressNextRelease  = true;  // Don't fire sequence advance on chord release
    }
    if (!resetChordTriggered &&
        (now - resetChordStartMs >= device_config::kResetHoldMs)) {
      resetChordTriggered = true;
      resetToBeginning();
    }
  } else if (!powerSwitch.isPressed() && !nextSwitch.isPressed()) {
    resetChordStartMs    = 0;
    resetChordTriggered  = false;
    suppressPowerRelease = false;
    suppressNextRelease  = false;
  }

  // --- Individual button events ----------------------------------------------
  if (previousSwitch.wasReleased() && !suppressPreviousRelease) {
    setSequence(previousSequenceValue(currentSequence));
  }

  if (powerSwitch.wasReleased() && !suppressPowerRelease) {
    outputEnabled = !outputEnabled;
    printSequenceStatus();
  }

  if (nextSwitch.wasReleased() && !suppressNextRelease) {
    setSequence(nextSequenceValue(currentSequence));
  }
}

void updatePeltier(uint32_t now, bool beamEnabled) {
  if (peltierOverride == OVERRIDE_FORCE_ON) {
    digitalWrite(device_config::kPeltierControlPin, HIGH);
    peltierHoldUntilMs = now + device_config::kPeltierPostBeamHoldMs;
    return;
  }

  if (peltierOverride == OVERRIDE_FORCE_OFF) {
    peltierHoldUntilMs = 0;
    digitalWrite(device_config::kPeltierControlPin, LOW);
    return;
  }

  if (beamEnabled) {
    digitalWrite(device_config::kPeltierControlPin, HIGH);
    peltierHoldUntilMs = now + device_config::kPeltierPostBeamHoldMs;
    return;
  }

  const bool keepCooling = static_cast<int32_t>(peltierHoldUntilMs - now) > 0;
  digitalWrite(device_config::kPeltierControlPin, keepCooling ? HIGH : LOW);
}

// =============================================================================
// NEOPIXEL UPDATE — applies CoreFrame animation to the NeoPixel strip.
// Called every loop iteration with the current timestamp and frame data.
// =============================================================================
void updateNeoPixel(uint32_t now, const CoreFrame &frame) {
  // Return early if mode is OFF or if output is disabled.
  if (frame.mode == orciny::CORE_MODE_OFF) {
    neoPixelStrip.clear();
    neoPixelStrip.show();
    return;
  }

  // Safety cap: ensure brightness is within current limit.
  const uint8_t cappedBrightness = min(frame.brightness,
                                       device_config::kMaxBrightnessForCurrentLimit);

  switch (frame.mode) {
    // --- EMBER mode: warm orange flicker across the strip -------------------
    case orciny::CORE_MODE_EMBER: {
      const uint8_t fFlicker = (sin8(now * frame.speed / 50U) + sin8(now * 19U + frame.speed * 3U)) / 2;
      const uint8_t level = map(fFlicker, 0, 255, 16, cappedBrightness);
      const uint32_t color = neoPixelStrip.Color(
          (frame.red * level) / 255,
          (frame.green * level) / 255,
          (frame.blue * level) / 255);
      for (uint16_t i = 0; i < neoPixelStrip.numPixels(); ++i) {
        neoPixelStrip.setPixelColor(i, color);
      }
      break;
    }

    // --- PULSE mode: solid color pulsing in and out -------------------------
    case orciny::CORE_MODE_PULSE: {
      const uint8_t pulseWave = triwave8(now / max(1U, (260U - frame.speed) / 4));
      const uint8_t level = map(pulseWave, 0, 255, 32, cappedBrightness);
      const uint32_t color = neoPixelStrip.Color(
          (frame.red * level) / 255,
          (frame.green * level) / 255,
          (frame.blue * level) / 255);
      for (uint16_t i = 0; i < neoPixelStrip.numPixels(); ++i) {
        neoPixelStrip.setPixelColor(i, color);
      }
      break;
    }

    // --- BEAM mode: beam-linked animation (matches beam colour) -----
    case orciny::CORE_MODE_BEAM: {
      const uint8_t level = map(sin8(now * frame.speed / 50U), 0, 255, 24, cappedBrightness);
      const uint32_t color = neoPixelStrip.Color(
          (frame.red * level) / 255,
          (frame.green * level) / 255,
          (frame.blue * level) / 255);
      for (uint16_t i = 0; i < neoPixelStrip.numPixels(); ++i) {
        neoPixelStrip.setPixelColor(i, color);
      }
      break;
    }

    // --- CLAW mode: trailing indicator following claw position -------
    case orciny::CORE_MODE_CLAW: {
      const uint8_t tailLength = max(1U, device_config::kNeoPixelCount / 8);
      const uint32_t baseColor = neoPixelStrip.Color(frame.red, frame.green, frame.blue);
      neoPixelStrip.clear();
      // Animate a trailing tail down the strip based on speed/time.
      const uint16_t headPos = ((now / 20U) * frame.speed / 100U) % device_config::kNeoPixelCount;
      for (uint8_t t = 0; t < tailLength; ++t) {
        const uint16_t pos = (headPos + device_config::kNeoPixelCount - t) % device_config::kNeoPixelCount;
        const uint8_t fadeFactor = (tailLength > 0) ? (255 * t / tailLength) : 255;
        neoPixelStrip.setPixelColor(pos, neoPixelStrip.Color(
            (frame.red * fadeFactor) / 510U,
            (frame.green * fadeFactor) / 510U,
            (frame.blue * fadeFactor) / 510U));
      }
      break;
    }

    // --- SHOW mode: rainbow color wheel animation ---------
    case orciny::CORE_MODE_SHOW: {
      for (uint16_t i = 0; i < neoPixelStrip.numPixels(); ++i) {
        // Hue varies by pixel position and time, creating a flowing rainbow.
        const uint8_t hue = (now / 10U) + (i * 5U);
        const uint32_t color = neoPixelStrip.ColorHSV(
            (hue << 8),              // Hue (0–65535 maps to 0–360 degrees)
            255,                      // Saturation (255 = fully saturated)
            cappedBrightness * 2);   // Value (brightness, scaled up)
        neoPixelStrip.setPixelColor(i, color);
      }
      break;
    }

    default:
      neoPixelStrip.clear();
      break;
  }

  // Push the buffered pixel data to the strip.
  neoPixelStrip.show();
}

// Helper: triangle wave generator (0–255, period in ms).
uint8_t triwave8(uint16_t elapsedMs) {
  const uint16_t cycleMs = 500;  // 500ms cycle = ~1 Hz
  const uint16_t phaseMs = elapsedMs % cycleMs;
  if (phaseMs < cycleMs / 2) {
    return (phaseMs * 510) / cycleMs;  // Ramp up
  } else {
    return 510 - (phaseMs * 510) / cycleMs;  // Ramp down
  }
}

// Helper: sine wave generator (0–255).
uint8_t sin8(uint32_t input) {
  input = input % 256;
  static const uint8_t sineTable[256] PROGMEM = {
    128, 131, 134, 137, 140, 143, 146, 149, 152, 155, 158, 161, 164, 167, 170, 173,
    176, 179, 182, 185, 188, 191, 194, 197, 199, 202, 205, 208, 210, 213, 216, 218,
    221, 223, 226, 228, 231, 233, 235, 238, 240, 242, 244, 246, 248, 250, 251, 253,
    254, 255, 255, 255, 255, 255, 255, 255, 255, 255, 255, 255, 255, 255, 255, 255,
    255, 255, 255, 255, 255, 255, 255, 255, 255, 255, 255, 255, 254, 253, 251, 250,
    248, 246, 244, 242, 240, 238, 235, 233, 231, 228, 226, 223, 221, 218, 216, 213,
    210, 208, 205, 202, 199, 197, 194, 191, 188, 185, 182, 179, 176, 173, 170, 167,
    164, 161, 158, 155, 152, 149, 146, 143, 140, 137, 134, 131, 128, 125, 122, 119,
    116, 113, 110, 107, 104, 101,  98,  95,  92,  89,  86,  83,  80,  77,  74,  71,
     68,  65,  62,  59,  57,  54,  51,  48,  46,  43,  40,  37,  35,  32,  29,  27,
     24,  22,  19,  17,  15,  12,  10,   8,   6,   4,   2,   1,   0,   0,   0,   0,
      0,   0,   1,   2,   4,   6,   8,  10,  12,  15,  17,  19,  22,  24,  27,  29,
     32,  35,  37,  40,  43,  46,  48,  51,  54,  57,  59,  62,  65,  68,  71,  74,
     77,  80,  83,  86,  89,  92,  95,  98, 101, 104, 107, 110, 113, 116, 119, 122,
    125, 128, 131, 134, 137, 140, 143, 146, 149, 152, 155, 158, 161, 164, 167, 170,
    173, 176, 179, 182, 185, 188, 191, 194, 197, 199, 202, 205, 208, 210, 213, 216
  };
  return pgm_read_byte(&sineTable[input]);
}

// =============================================================================
// EFFECT UPDATE — applies the active EffectCommand to all hardware outputs.

// Called every loop iteration with the current timestamp.
// =============================================================================
void updateEffects(uint32_t now, const EffectCommand &command) {

  // Gate every subsystem on the master outputEnabled flag from the command.
  const bool sparksEnabled = command.outputEnabled && command.sparksEnabled;
  const bool beamEnabled   = command.outputEnabled && command.beamEnabled;
  const bool clawEnabled   = command.outputEnabled && command.clawEnabled;
  const bool beamAnyForcedOn =
      (beamRedOverride == OVERRIDE_FORCE_ON) ||
      (beamGreenOverride == OVERRIDE_FORCE_ON) ||
      (beamBlueOverride == OVERRIDE_FORCE_ON);
  const bool beamForCooling = beamEnabled || (command.outputEnabled && beamAnyForcedOn);

  for (uint8_t i = 0; i < device_config::kSparkCount; ++i) {
    if (isSparkTestActive()) {
      sparks[i].setManualLevel(isSparkTestChannelEnabled(i) ? 255 : 0);
      continue;
    }
    sparks[i].update(now, sparksEnabled, command.sparksIntensity);
  }
  beamEffect.update(now, beamEnabled);

  // Per-channel debug override is applied after the base beam effect writes PWM.
  if (!command.outputEnabled || beamRedOverride == OVERRIDE_FORCE_OFF) {
    analogWrite(device_config::kPropMakerLed1Pin, 0);
  } else if (beamRedOverride == OVERRIDE_FORCE_ON) {
    analogWrite(device_config::kPropMakerLed1Pin, 255);
  }

  if (!command.outputEnabled || beamGreenOverride == OVERRIDE_FORCE_OFF) {
    analogWrite(device_config::kPropMakerLed2Pin, 0);
  } else if (beamGreenOverride == OVERRIDE_FORCE_ON) {
    analogWrite(device_config::kPropMakerLed2Pin, 255);
  }

  if (!command.outputEnabled || beamBlueOverride == OVERRIDE_FORCE_OFF) {
    analogWrite(device_config::kPropMakerLed3Pin, 0);
  } else if (beamBlueOverride == OVERRIDE_FORCE_ON) {
    analogWrite(device_config::kPropMakerLed3Pin, 255);
  }

  updatePeltier(now, beamForCooling);
  clawEffect.update(now, clawEnabled);
}

// =============================================================================
// SETUP
// Runs once at power-on or after a reset.  Initialises every subsystem in order.
// =============================================================================
void setup() {
  // Start USB serial console (appears on the Arduino IDE Serial Monitor).
  Serial.begin(device_config::kUsbBaudRate);

  // Initialise I2C bus required by the Servo FeatherWing.
  Wire.begin();
  servoDriver.begin();
  servoDriver.setPWMFreq(50);  // 50 Hz is standard for hobby servos

  // Seed the random number generator with an unconnected analog pin noise value.
  // This prevents the spark timing pattern from being identical every boot.
  randomSeed(analogRead(A0));

  // IMPORTANT: the Prop-Maker PWR pin must be driven HIGH before any MOSFET
  // output will work.  If this line is omitted, sparks and beam stay silent.
  pinMode(device_config::kPropMakerPwrPin, OUTPUT);
  digitalWrite(device_config::kPropMakerPwrPin, HIGH);
  pinMode(device_config::kPeltierControlPin, OUTPUT);
  digitalWrite(device_config::kPeltierControlPin, LOW);

  // Initialise switch debouncers before handleSwitches() is ever called.
  powerSwitch.begin(device_config::kPowerSwitchPin);
  previousSwitch.begin(device_config::kPreviousSwitchPin);
  nextSwitch.begin(device_config::kNextSwitchPin);

  // Initialise all four spark channels on their respective GPIO pins.
  for (uint8_t i = 0; i < device_config::kSparkCount; ++i) {
    sparks[i].begin(device_config::kSparkPins[i]);
  }

  // Initialise the Prop-Maker beam effect with the three MOSFET LED pins.
  beamEffect.begin(device_config::kPropMakerLed1Pin,
                   device_config::kPropMakerLed2Pin,
                   device_config::kPropMakerLed3Pin);

  // Initialise the claw with servo driver reference, channel numbers, and travel limits.
  clawEffect.begin(servoDriver,
                   device_config::kServoChannelA,
                   device_config::kServoChannelB,
                   device_config::kServoAMinAngle,
                   device_config::kServoAMaxAngle,
                   device_config::kServoBMinAngle,
                   device_config::kServoBMaxAngle);

  // Initialise the NeoPixel strip on GP4.
  neoPixelStrip.begin();
  neoPixelStrip.setBrightness(device_config::kMaxBrightnessForCurrentLimit);
  neoPixelStrip.clear();  // Start all pixels off
  neoPixelStrip.show();

  Serial.println(F("FX demo ready (standalone-only mode)."));
  printHelp();
  printSequenceStatus();
}

// =============================================================================
// LOOP
// Runs repeatedly after setup().  Keep it fast — no delay() calls.
//
// Standalone-only: handleSwitches(), handleUsbCommands(), and
// buildActiveProfile() drive all outputs.
// =============================================================================
void loop() {
  const uint32_t now = millis();

  // Always service USB commands and switch debouncers.
  handleUsbCommands();
  handleSwitches(now);

  const SceneProfile profile = buildActiveProfile();
  beamEffect.setPalette(getPaletteForId(
      beamPaletteOverride == BEAM_PALETTE_AUTO
          ? profile.beamPaletteId
          : beamPaletteOverride));
  updateEffects(now, profileToEffectCommand(profile));
  const CoreFrame &frameToRender =
      (neoPixelOverride.mode != orciny::CORE_MODE_OFF)
          ? neoPixelOverride
          : profile.coreFrame;
  updateNeoPixel(now, frameToRender);
}
